MOSH-Insa-Toulouse/2025-2026-4GPb-NMinhKhue-lok411-ntruonginsatls/LTSPice/wiring.asc

C1: cap; 100n
C2: cap; 100n
C3: cap; {C3}
C5: cap; 1p
R1: res; 100k
R2: res; {R2}
R4: res; 100k
R5: res; 10k
R6: res; 1k
U1: LTC1050
V1: voltage; SINE(0 325 50)
V2: voltage; 5
V3: voltage; PULSE(0 1 0.2 0.1 0.1 2); AC 1
X1: capteur_graphite
Named nets: 0, ADC
.tran 5
.step param C3 0.5µ 2µ 0.5µ
.step param R3 0.5k 2k 0.5k
