MOSH-Insa-Toulouse/2025-2026-4GPb-NMinhKhue-lok411-ntruonginsatls/LTSPice/capteur_graphite.asc

B1: bi; I=V(cp,cn)*(10n + V(gc, gn)*10n)
C1: cap; 200µ
R1: res; 1k
Named nets: gp, gn, gc, cp, cn
